MadsRudolph/surround-speaker-mount/output_blender/terminal_clearance.png

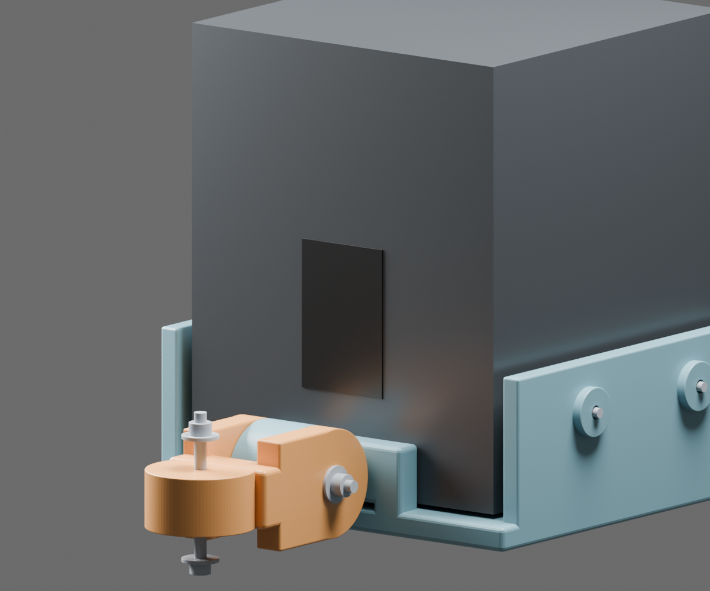
output_blender/terminal_clearance.png
