MadsRudolph/surround-speaker-mount/rail-mount/render/overview-preview.png

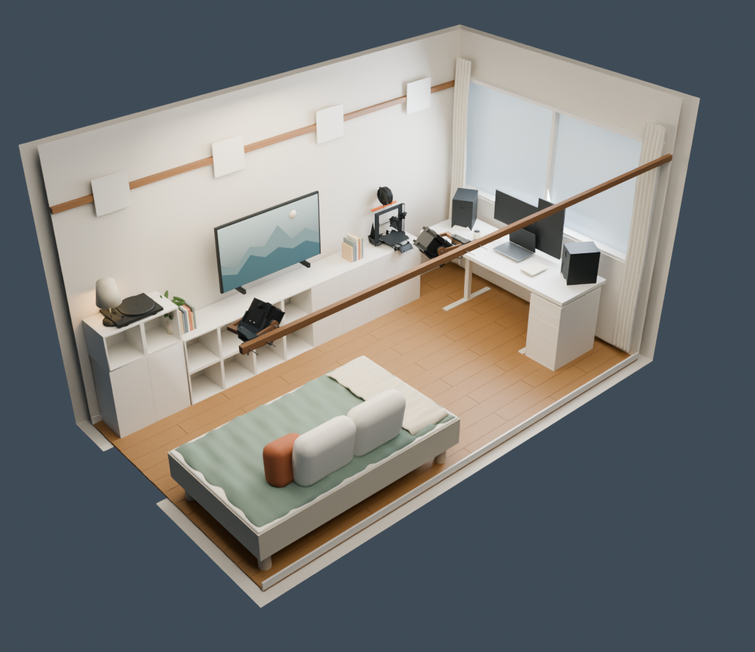
rail-mount/render/overview-preview.png
