MadsRudolph/surround-speaker-mount/output_blender/assembly.png

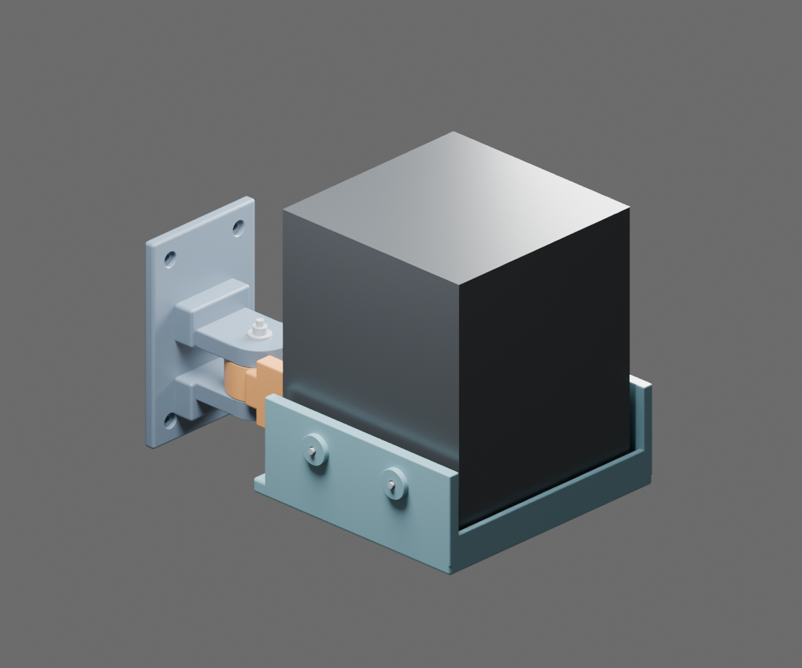
output_blender/assembly.png
